SKZBadHabit/MMOrtho/images/01.png

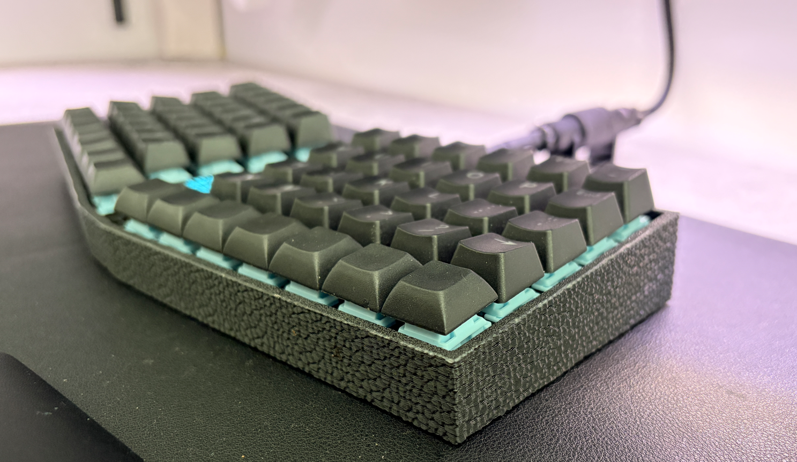
images/01.png
